jonpodtu/SmartLunchbox/renderings/Blue.png

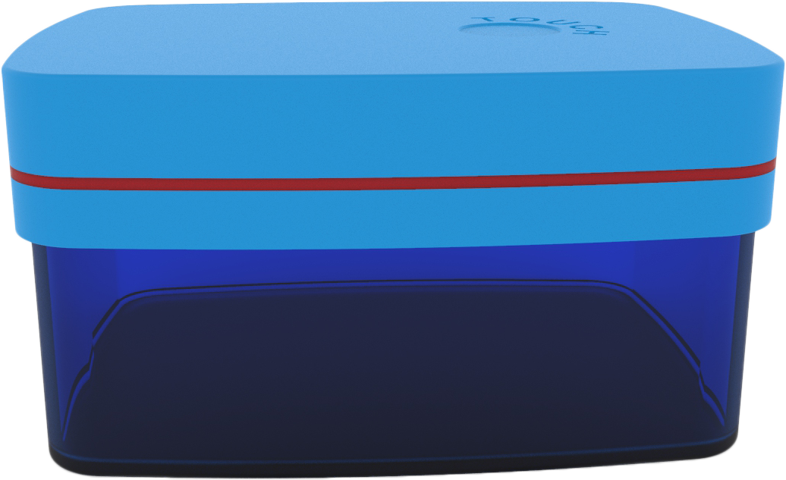
renderings/Blue.png
