jonpodtu/SmartLunchbox/renderings/Foodbox1 lights on.jpg

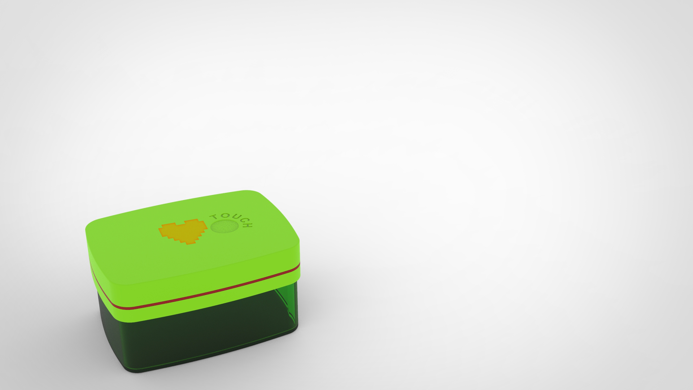
renderings/Foodbox1 lights on.jpg
