jonpodtu/SmartLunchbox/renderings/green w backgrund.jpg

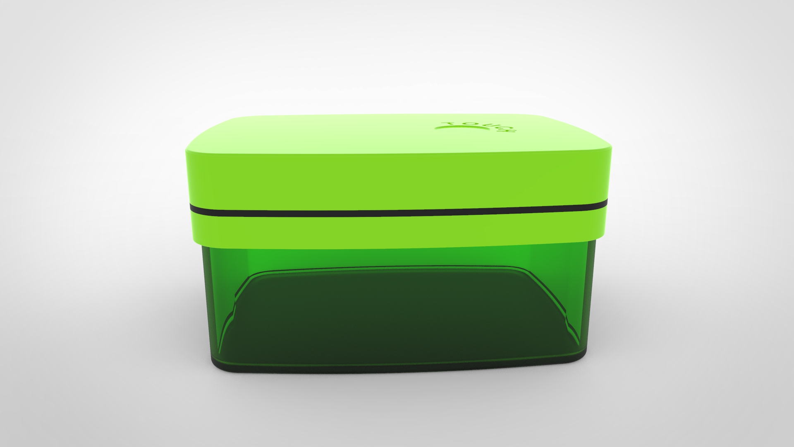
renderings/green w backgrund.jpg
