jonpodtu/SmartLunchbox/renderings/Green.png

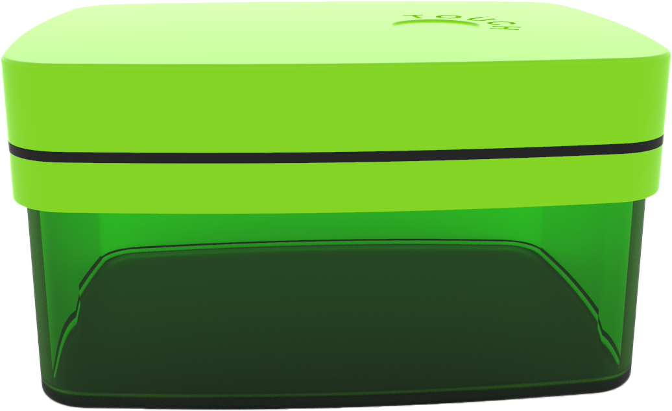
renderings/Green.png
