jonpodtu/SmartLunchbox/renderings/Ontable.jpg

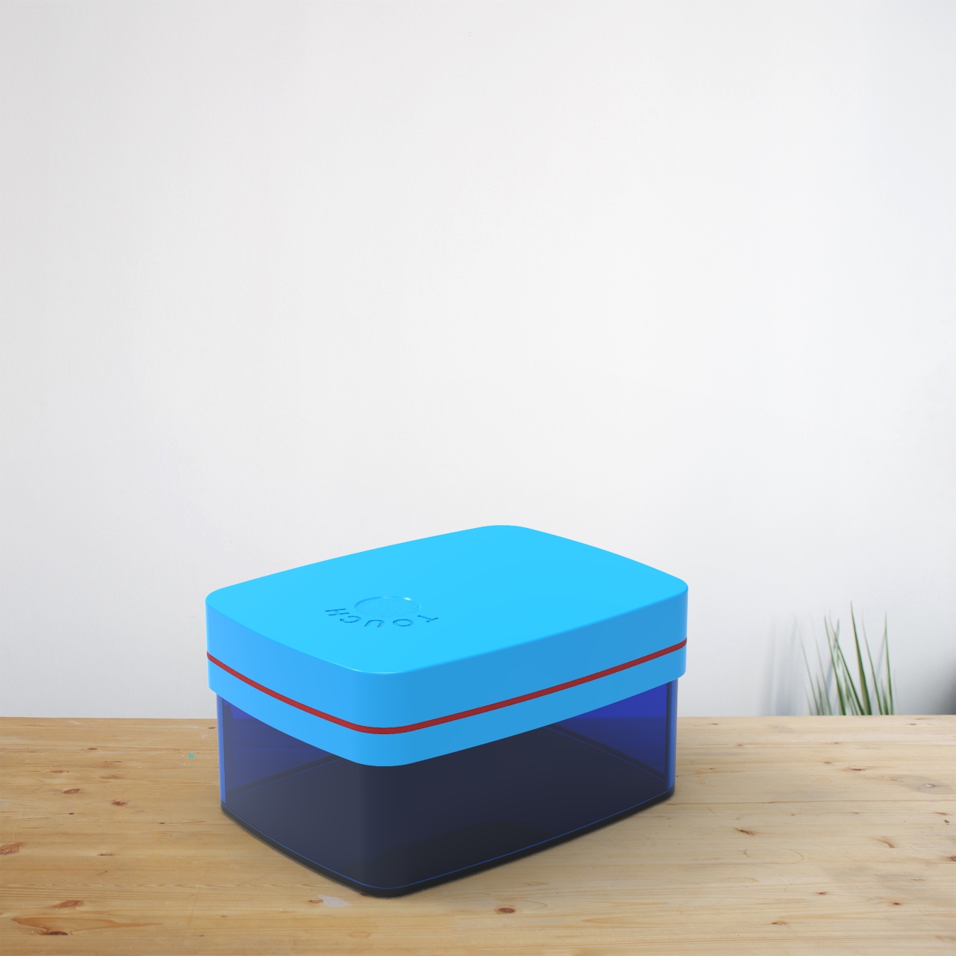
renderings/Ontable.jpg
