jonpodtu/SmartLunchbox/renderings/Red.png

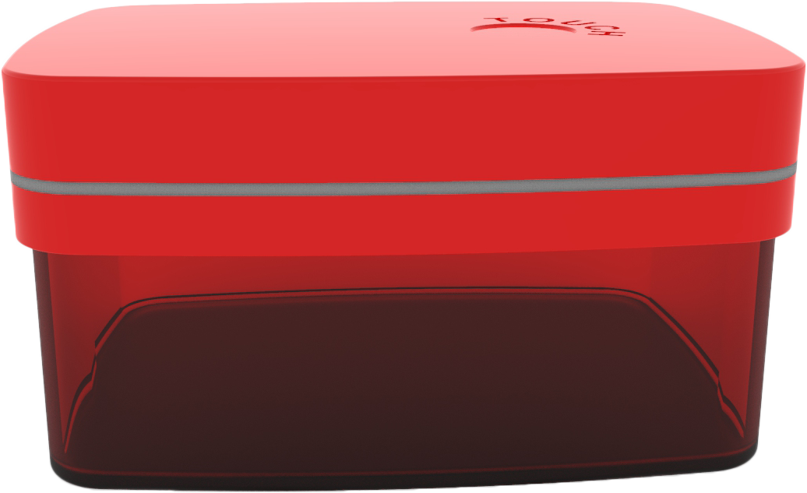
renderings/Red.png
