jonpodtu/SmartLunchbox/ThingSpeak/talkback.jpg

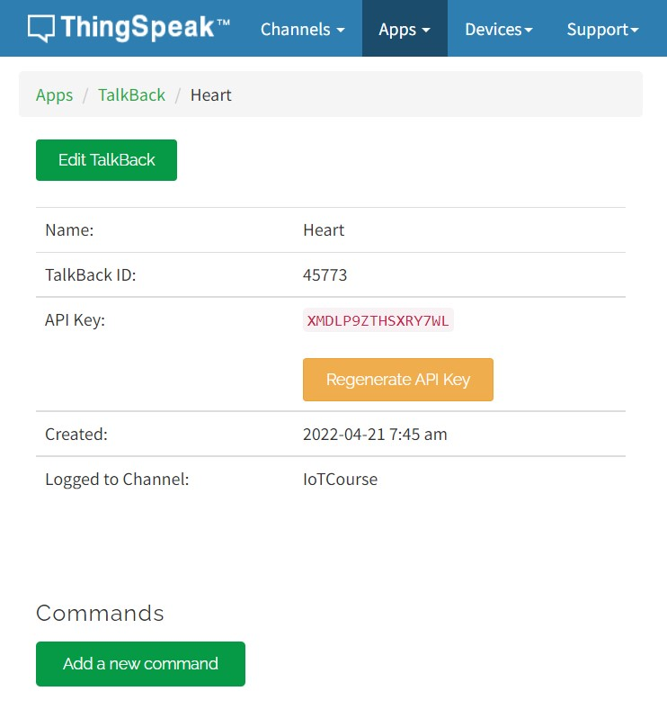
ThingSpeak/talkback.jpg
