jonpodtu/SmartLunchbox/fritzing/Project_setup_bb.png

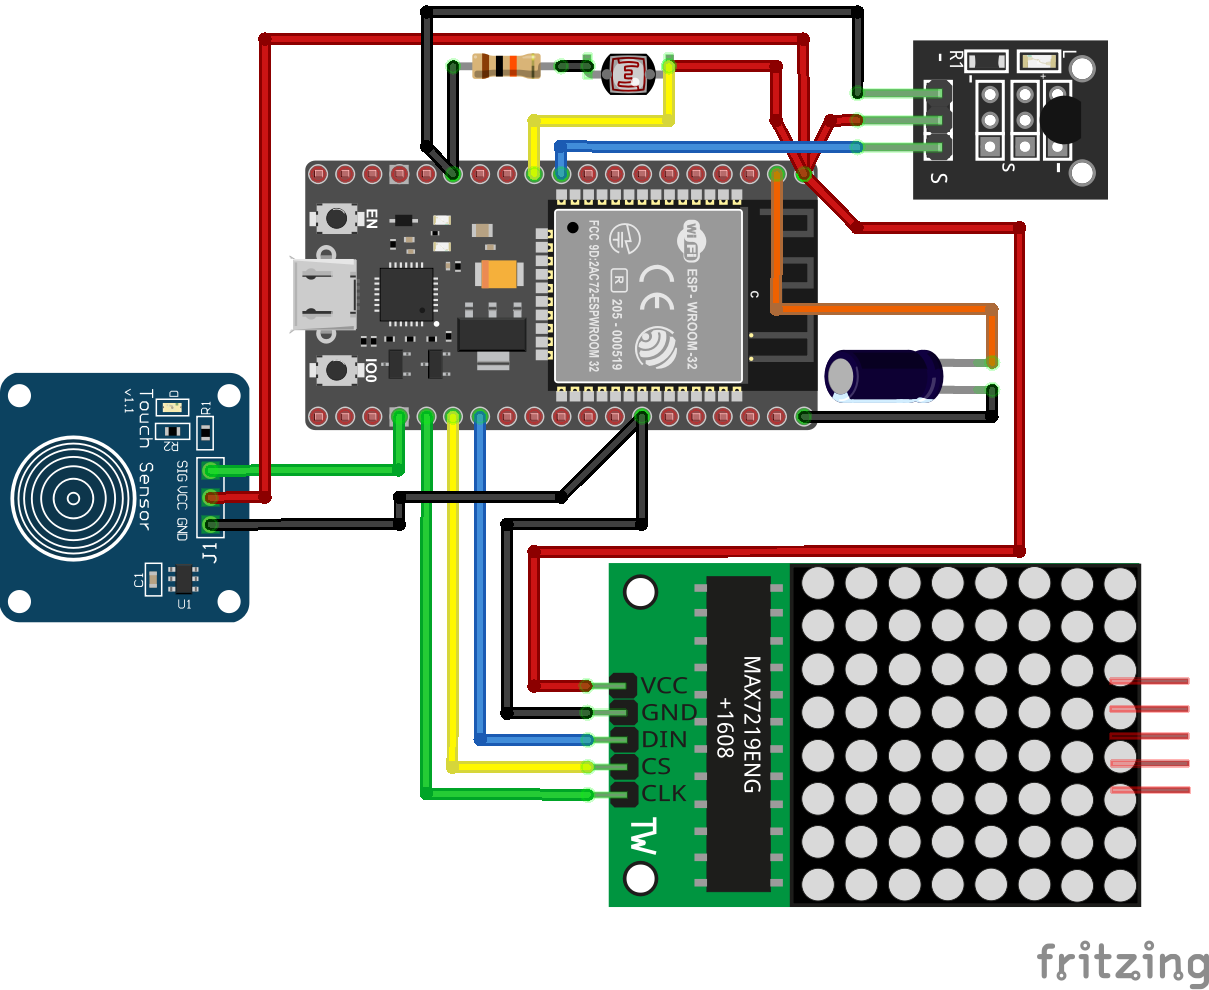
fritzing/Project_setup_bb.png
